RaniSargees/pcb-businesscard/firmware/Source/User/hk32f030m_it.c

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

/* Includes ------------------------------------------------------------------*/
#include "hk32f030m_it.h"
#include "hk32f030m_tim.h"
#include "hardware.h"

/* External variables --------------------------------------------------------*/

/******************************************************************************/
/*           Cortex-M0 Processor Interruption and Exception Handlers          */ 
/******************************************************************************/
/**
  * @brief This function handles Non maskable interrupt.
  */
void NMI_Handler(void)
{
}

/**
  * @brief This function handles Hard fault interrupt.
  */
void HardFault_Handler(void)
{
  while (1)
  {
  }
}

/**
  * @brief This function handles System service call via SWI instruction.
  */
void SVC_Handler(void)
{
}

/**
  * @brief This function handles Pendable request for system service.
  */
void PendSV_Handler(void)
{
}

/**
  * @brief This function handles System tick timer.
  */
void SysTick_Handler(void)
{
}

/******************************************************************************/
/* hk32f030m Peripheral Interrupt Handlers                                    */
/* Add here the Interrupt Handlers for the used peripherals.                  */
/* For the available peripheral interrupt handler names,                      */
/* please refer to the startup file (startup_hk32f030m.s).                    */
/******************************************************************************/

/* USER CODE BEGIN 1 */

void EXTI1_IRQHandler(void) {
	if (EXTI_GetITStatus(EXTI_Line1) != RESET) {
		EXTI_ClearITPendingBit(EXTI_Line1);
	}
}

//void EXTI2_IRQHandler(void) {
//	if (EXTI_GetITStatus(EXTI_Line2) != RESET) {
//		EXTI_ClearITPendingBit(EXTI_Line2);
//		SOFT_DELAY_SHORT
//	}
//}

//void TIM2_IRQHandler(void)
//{
//    if (TIM_GetITStatus(TIM2, TIM_IT_Update) != RESET)
//    {
//        TIM_ClearITPendingBit(TIM2, TIM_IT_Update);
//    }
//}
/* USER CODE END 1 */
/************************ (C) COPYRIGHT HKMicroChip *****END OF FILE****/
